WhereslyClock/MyWhereslyClock/markup/BiggerPictures/Eeek.jpg

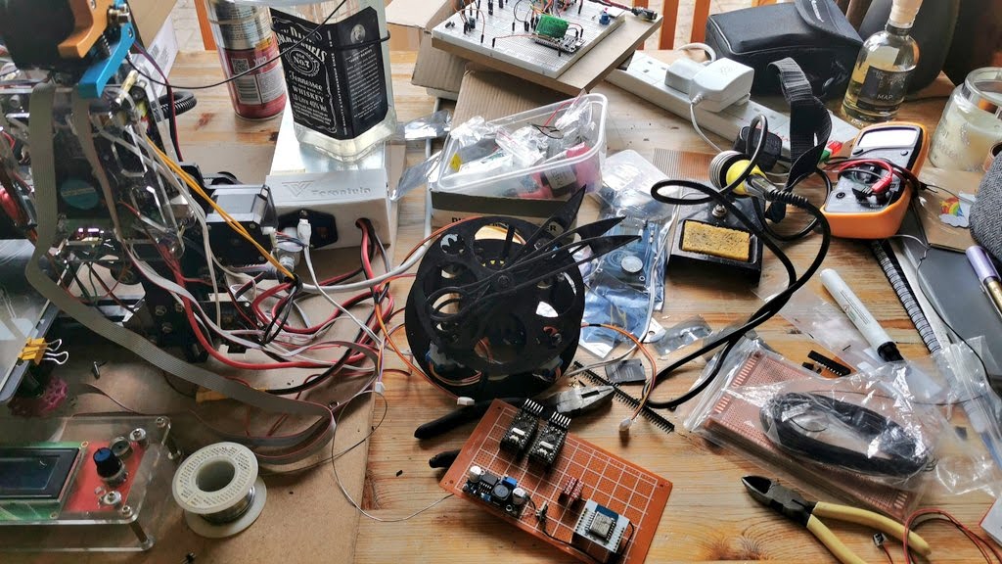
markup/BiggerPictures/Eeek.jpg
