WhereslyClock/MyWhereslyClock/markup/BiggerPictures/IMG_20210426_200710.jpg

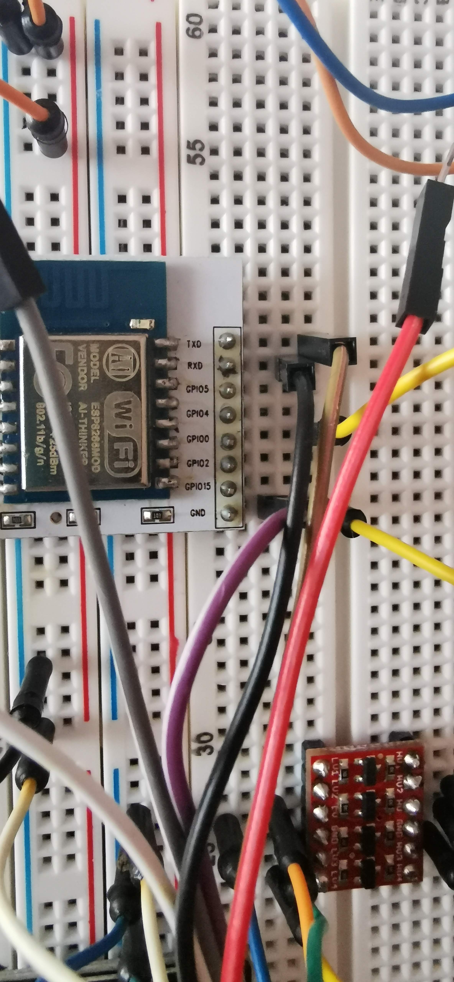
markup/BiggerPictures/IMG_20210426_200710.jpg
