WhereslyClock/MyWhereslyClock/markup/BiggerPictures/newclockdesign.png

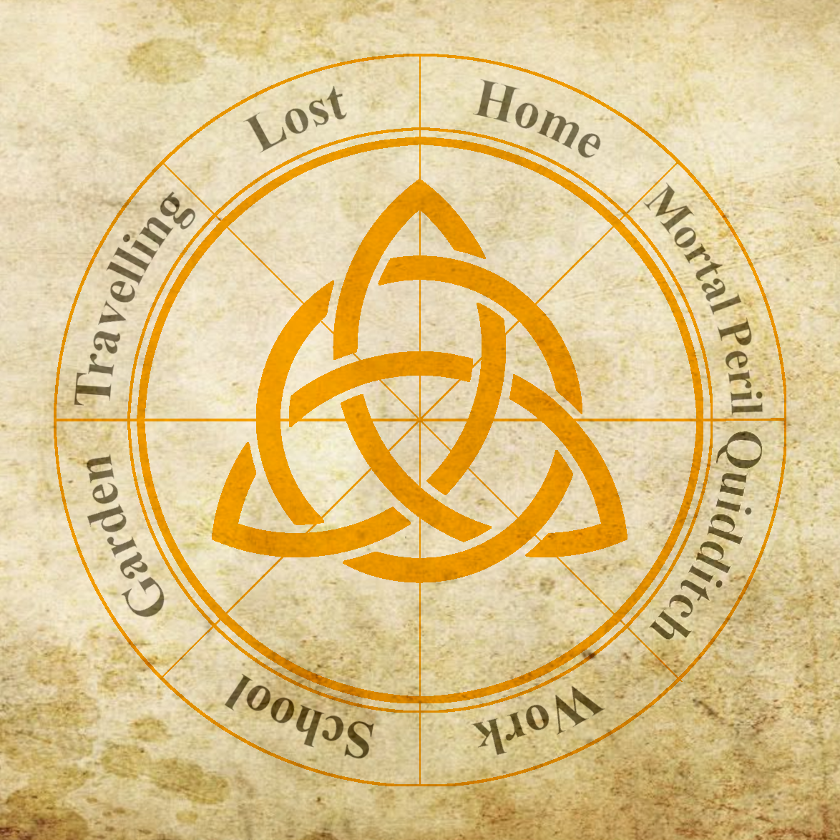
markup/BiggerPictures/newclockdesign.png
