WhereslyClock/MyWhereslyClock/markup/ot8.jpg

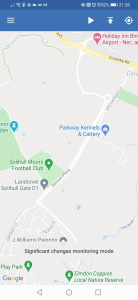
markup/ot8.jpg
