WhereslyClock/MyWhereslyClock/markup/WhereslyClockStill.png

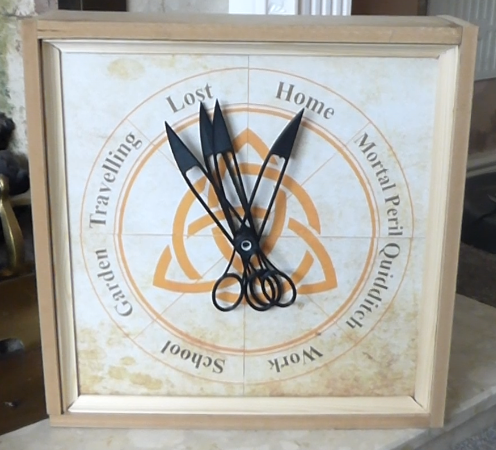
markup/WhereslyClockStill.png
